steveeidemiller/sensor-ambient/assets/soldering-2.jpg

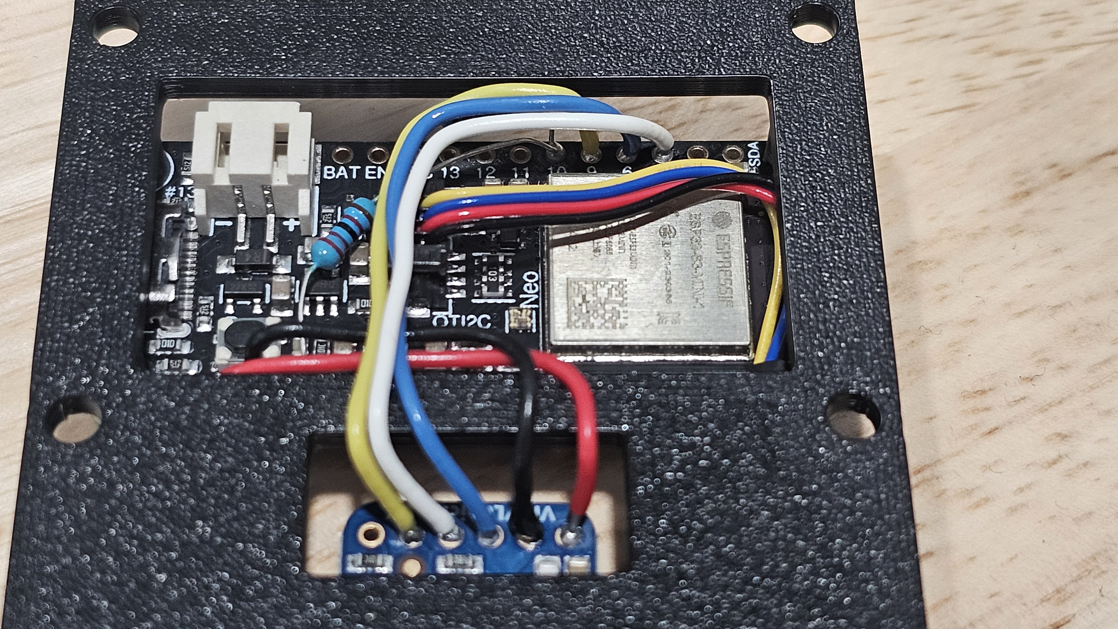
assets/soldering-2.jpg
